rfcx/rfcx-sentinel-pcb/Images/MPPT.png

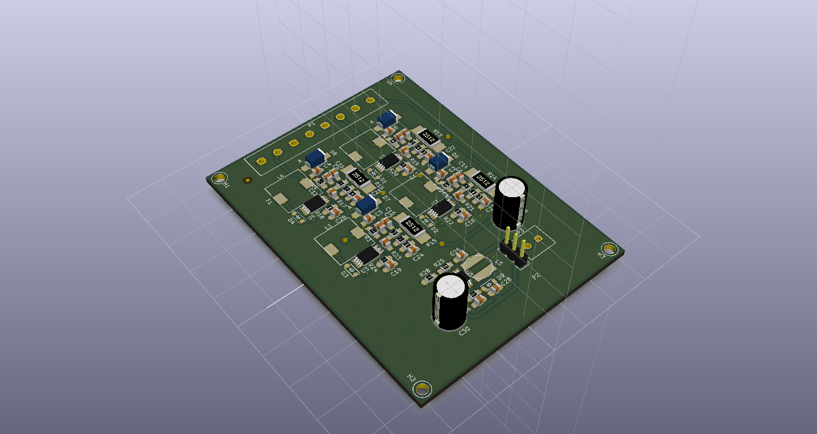
Images/MPPT.png
